InsaneDev27/DIY-Laptop-Mouse-Project/images/Right Click Button Glued.jpg

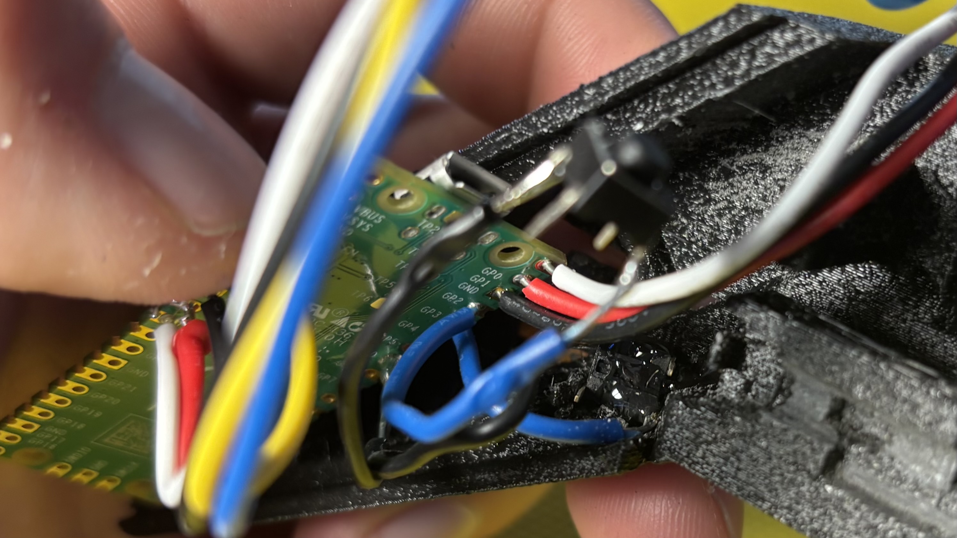
images/Right Click Button Glued.jpg
