InsaneDev27/DIY-Laptop-Mouse-Project/images/Screw Spread.jpg

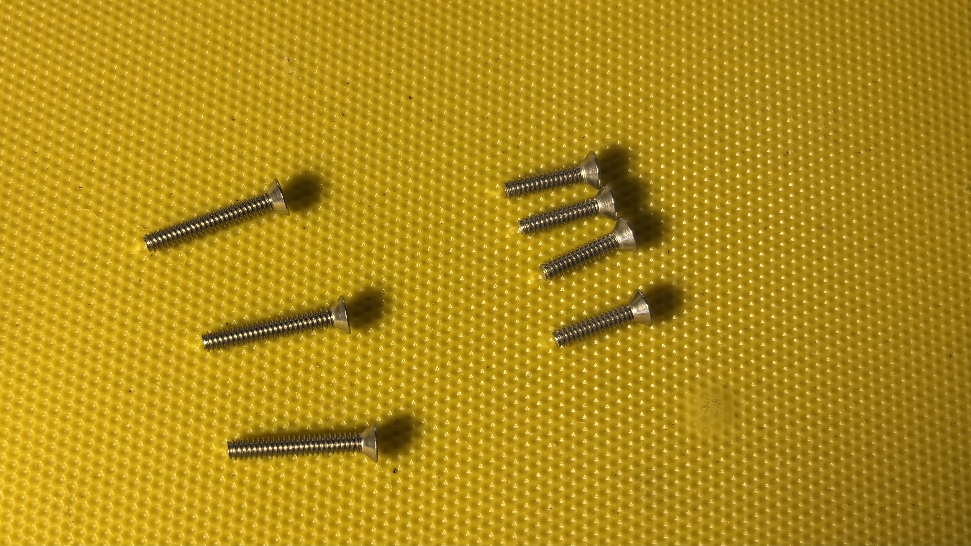
images/Screw Spread.jpg
