InsaneDev27/DIY-Laptop-Mouse-Project/images/Scroll Wheel Attached to Rotary Encoder.jpg

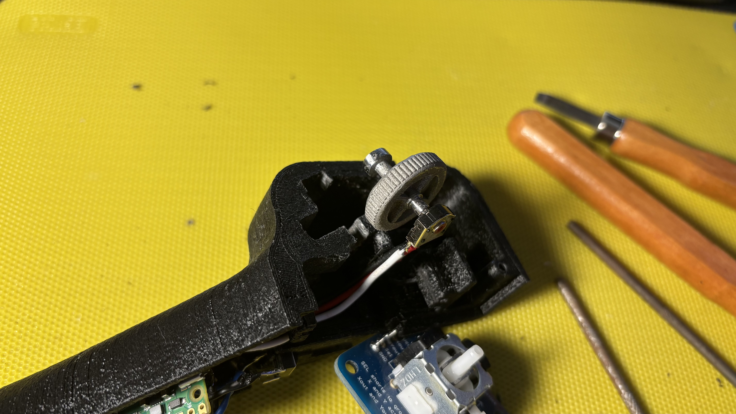
images/Scroll Wheel Attached to Rotary Encoder.jpg
