InsaneDev27/DIY-Laptop-Mouse-Project/images/Starting the Tap on Clamp Screw.jpg

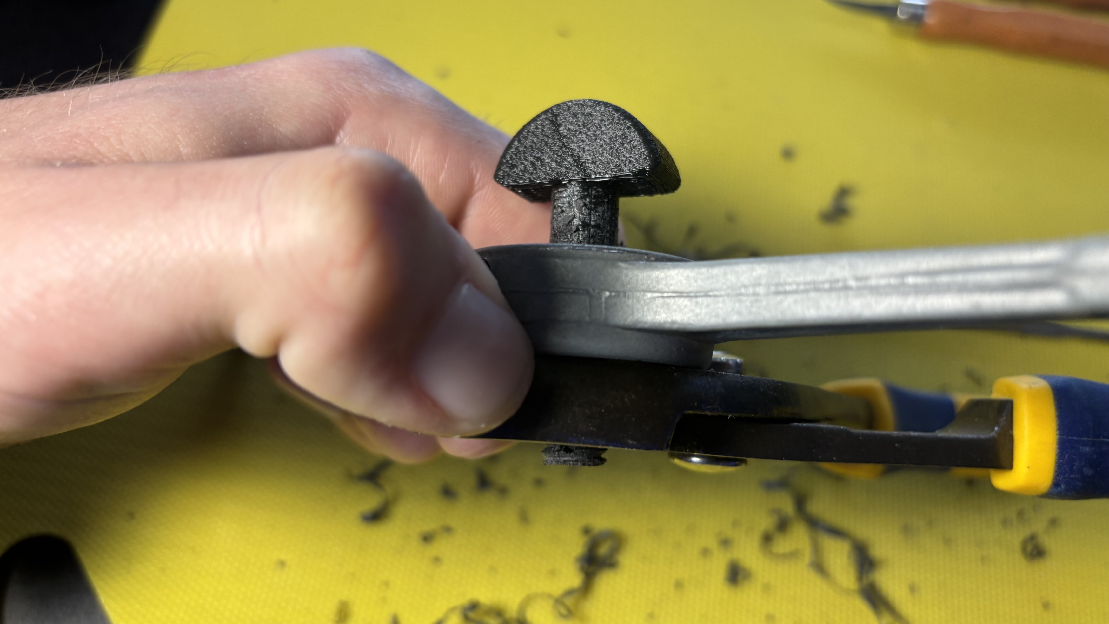
images/Starting the Tap on Clamp Screw.jpg
