InsaneDev27/DIY-Laptop-Mouse-Project/images/Installing Plunger Extender.jpg

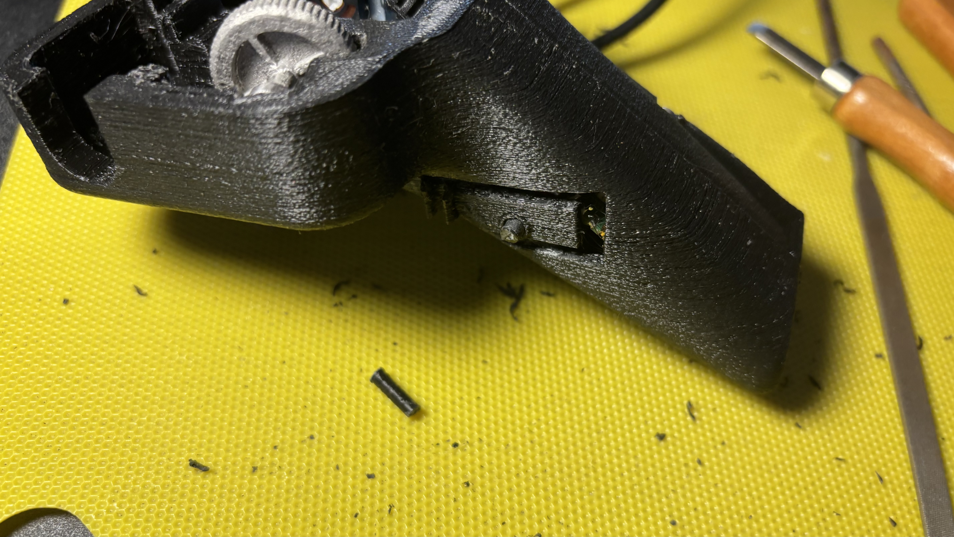
images/Installing Plunger Extender.jpg
